suda/medsgenie/OpenSCAD/MkII/tube.scad

include <constants.scad>;

module tube(pills=1) {
	difference() {
		cylinder(h=(pill_height * pills), r=(pill_diam + 2) / 2);
		translate([0, 0, -1])
			cylinder(h=(pill_height * pills) + 2, r=pill_diam / 2);
	}
//    translate([0, 0, -8])
//    difference() {
//		cylinder(h=11, r=(pill_diam + 4) / 2);
//		translate([0, 0, -1])
//			cylinder(h=7, r=(pill_diam + 2) / 2);
//        translate([0, 0, -1])
//			cylinder(h=12, r=pill_diam / 2);
//	}
}
